lysanderuy/Robocon-2025/Hardware/3D Parts/Resources/N20/втулка центральной шестерни.SLDPRT

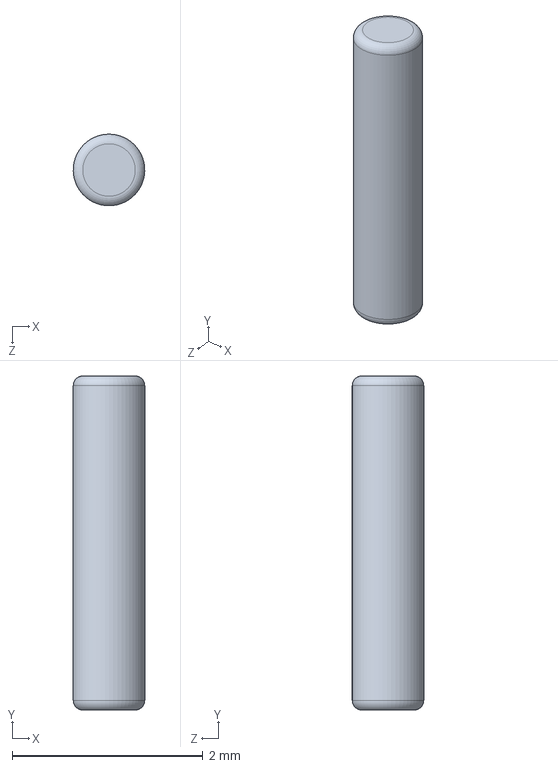
[picture p17: CAD file, 2025-04-21]
Hardware/3D Parts/Resources/N20/втулка центральной шестерни.SLDPRT
0.75 x 3.50 x 0.749 mm
