lysanderuy/Robocon-2025/Hardware/3D Parts/Resources/N20/втулка шестерни.SLDPRT

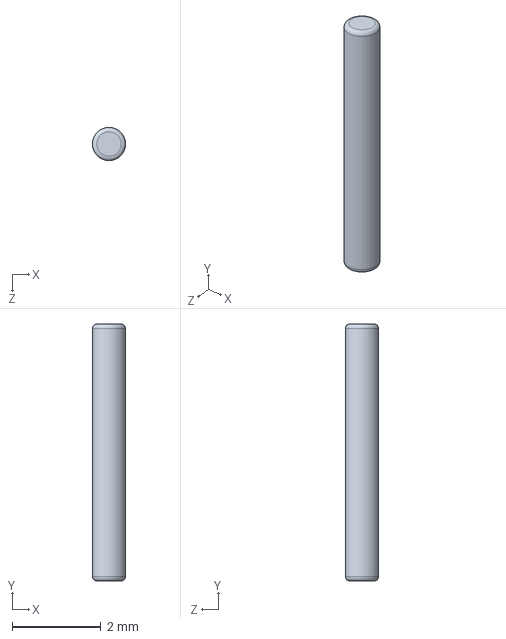
[picture p18: CAD file, 2025-04-21]
Hardware/3D Parts/Resources/N20/втулка шестерни.SLDPRT
0.748 x 5.80 x 0.75 mm
