lysanderuy/Robocon-2025/Hardware/3D Parts/Resources/N20/нижняя пластина редуктора.SLDPRT

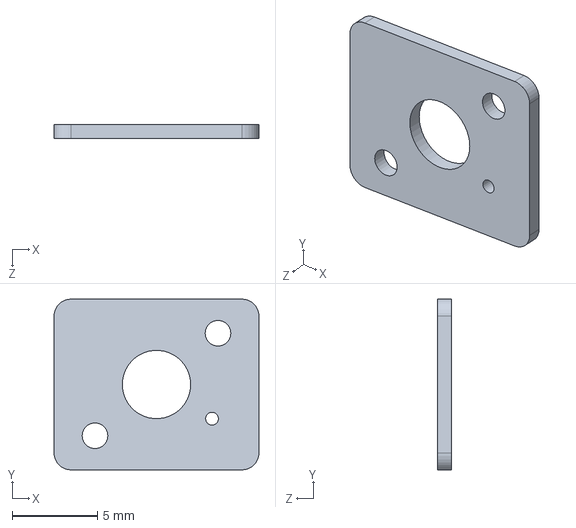
[picture p19: CAD file, 2025-04-21]
Hardware/3D Parts/Resources/N20/нижняя пластина редуктора.SLDPRT
12.0 x 10.0 x 0.8 mm
