lysanderuy/Robocon-2025/Hardware/3D Parts/Resources/N20/большая  фтулка.SLDPRT

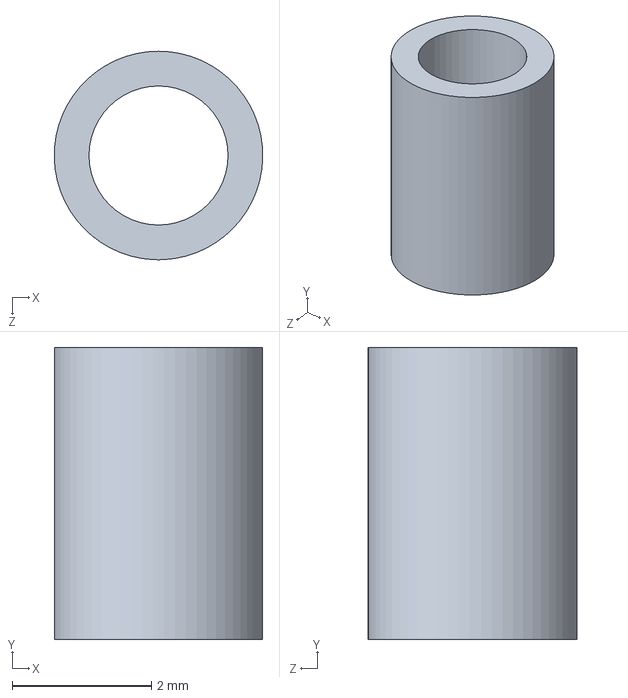
[picture p20: CAD file, 2025-04-21]
Hardware/3D Parts/Resources/N20/большая фтулка.SLDPRT
3.00 x 4.20 x 3.00 mm
